Anton-Augustsson/power-tool-workbench/cad/sorting-boxes/stl/2x4.stl

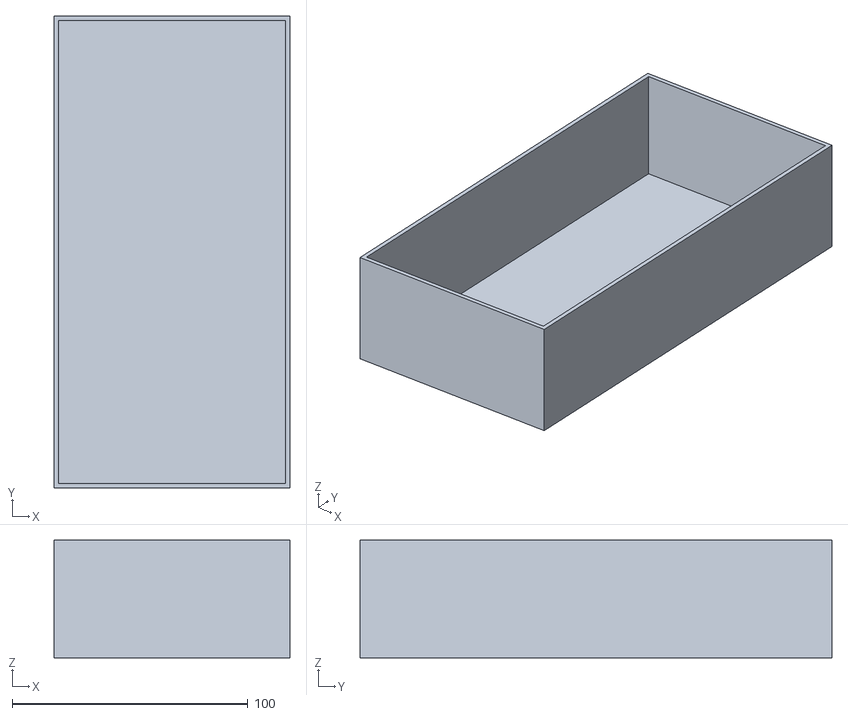
[picture p17: CAD file, 2020-06-16]
cad/sorting-boxes/stl/2x4.stl
100.0 x 200.0 x 50.0
