Anton-Augustsson/power-tool-workbench/cad/sorting-boxes/stl/4x4.stl

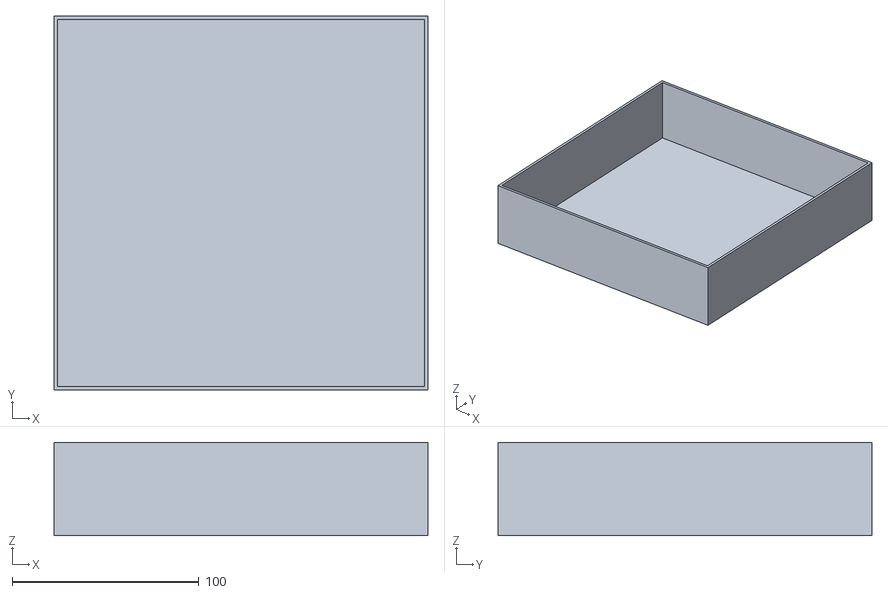
[picture p19: CAD file, 2020-06-16]
cad/sorting-boxes/stl/4x4.stl
200.0 x 200.0 x 50.0
