Anton-Augustsson/power-tool-workbench/cad/sorting-boxes/stl/3x3.stl

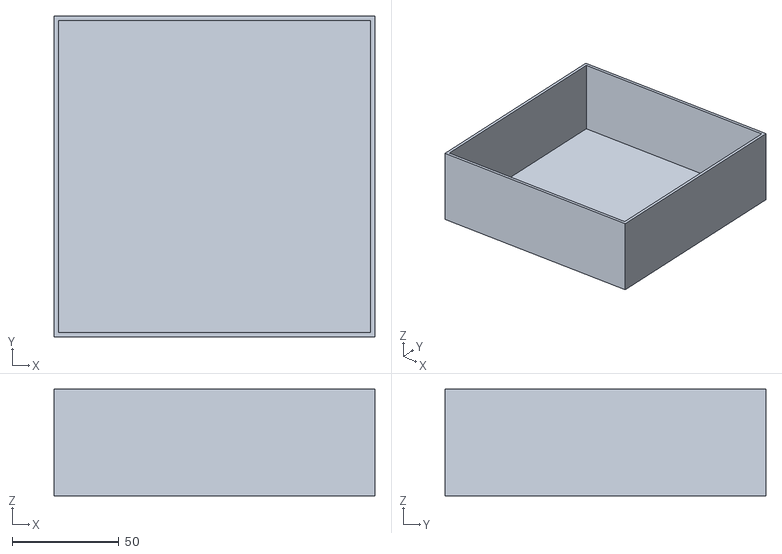
[picture p20: CAD file, 2020-06-16]
cad/sorting-boxes/stl/3x3.stl
150.0 x 150.0 x 50.0
