Anton-Augustsson/power-tool-workbench/cad/sorting-boxes/stl/1x4.stl

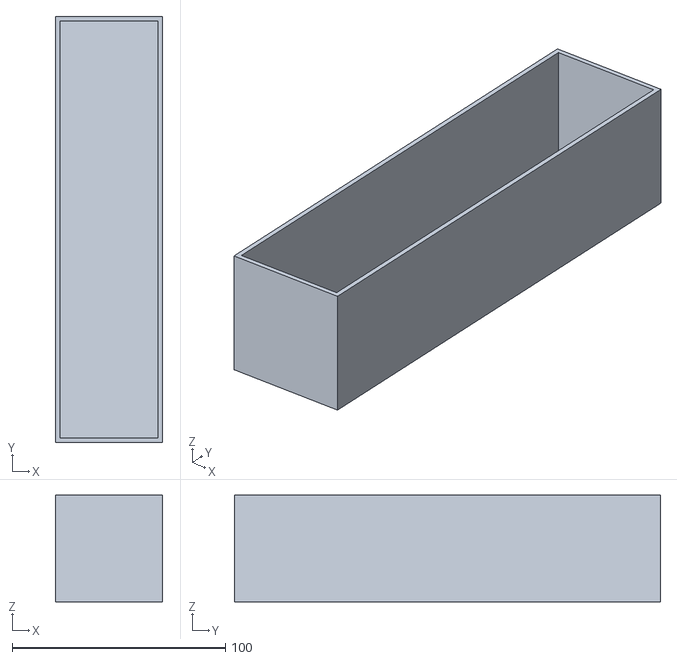
[picture p21: CAD file, 2020-06-16]
cad/sorting-boxes/stl/1x4.stl
50.0 x 200.0 x 50.0
