Anton-Augustsson/power-tool-workbench/cad/module/drawer-storage.scad

/*

    Drawer Storage
    
    By Anton Augustsson


*/

use <simple-drawer.scad>;
use <sliding-shelf.scad>;
use <storage-unit.scad>;

module drawerStorage (
    thickness,
    length,
    width,
    height,
    x,y,z,
    zRotate
    ){
/*
    ---------- Local varibles ---------- 
*/


storageUnitThickness = thickness;
storageUnitWidth     = width;
storageUnitLength    = length;
storageUnitHeight    = height;

thicknessBottom = thickness;
thicknessSide   = thickness;
thicknessFront  = 15;
        
slidingShelfWidth  = (length
        -thickness*2)/2-
        thickness/2;
slidingShelfLength = width
        -thickness*2;
slidingShelfHeight = height/3*2
        +9;

drawerWidth  = slidingShelfWidth;
drawerLength = slidingShelfLength;
drawerHeight = (height-2*thickness)/6;

/*
    ---------- Code ---------- 
*/

translate([
    x,
    y,
    z]) 
rotate([0,0,zRotate])
union () {

storageUnit (
    storageUnitThickness,
    storageUnitWidth,
    storageUnitLength,
    storageUnitHeight,
    0,0,0
    );

// Starting from lower corner    
// 1 Large    
simpleDrawer  (
    thicknessBottom,
    thicknessSide,
    thicknessFront,
    drawerLength,
    drawerWidth,
    drawerHeight*2,
    thickness,
    0,
    thickness
    );

// 2     
simpleDrawer  (
    thicknessBottom,
    thicknessSide,
    thicknessFront,
    drawerLength,
    drawerWidth,
    drawerHeight,
    thickness,
    0,
    thickness+drawerHeight*2
    );

// 3
simpleDrawer  (
    thicknessBottom,
    thicknessSide,
    thicknessFront,
    drawerLength,
    drawerWidth,
    drawerHeight,
    thickness,
    0,
    thickness+drawerHeight*3
    );

// 4
simpleDrawer  (
    thicknessBottom,
    thicknessSide,
    thicknessFront,
    drawerLength,
    drawerWidth,
    drawerHeight,
    thickness,
    0,
    thickness+drawerHeight*4
    );

// 5
simpleDrawer  (
    thicknessBottom,
    thicknessSide,
    thicknessFront,
    drawerLength,
    drawerWidth,
    drawerHeight,
    thickness,
    0,
    thickness+drawerHeight*5
    );



// 6 Large    
simpleDrawer  (
    thicknessBottom,
    thicknessSide,
    thicknessFront,
    drawerLength,
    drawerWidth,
    drawerHeight*2,
    thickness*2
    +slidingShelfWidth,
    0,
    thickness
    );

// 7
simpleDrawer  (
    thicknessBottom,
    thicknessSide,
    thicknessFront,
    drawerLength,
    drawerWidth,
    drawerHeight,
    thickness*2
    +slidingShelfWidth,
    0,
    thickness+drawerHeight*2
    );

// 8
simpleDrawer  (
    thicknessBottom,
    thicknessSide,
    thicknessFront,
    drawerLength,
    drawerWidth,
    drawerHeight,
    thickness*2
    +slidingShelfWidth,
    0,
    thickness+drawerHeight*3
    );    

// 9
simpleDrawer  (
    thicknessBottom,
    thicknessSide,
    thicknessFront,
    drawerLength,
    drawerWidth,
    drawerHeight,
    thickness*2
    +slidingShelfWidth,
    0,
    thickness+drawerHeight*4
    );    

// 10
simpleDrawer  (
    thicknessBottom,
    thicknessSide,
    thicknessFront,
    drawerLength,
    drawerWidth,
    drawerHeight,
    thickness*2
    +slidingShelfWidth,
    0,
    thickness+drawerHeight*5
    );    

}}
    
/*
    ---------- Example ---------- 
*/


standardSheathingWidth = 1220; 
standardSheathingLength = 2440;

mdfTopThickness = 19;
plywoodTopThickness = 12;

// Side protection for ply and mdf
edgeTopThickness = 20; 
edgeTopWidth = 167;
edgeTopLengthX = standardSheathingLength
    +2*edgeTopThickness;
edgeTopLengthY = standardSheathingWidth
    +2*edgeTopThickness;

// 4 list betweend mdf and ply (Pine)
listTopThickness = 20; 
listTopWidth = 80;
listTopLengthX = standardSheathingLength/4
    -listTopThickness;
listTopLengthY = standardSheathingWidth;

// 6 legs (Pine)
legLength = 900
    -plywoodTopThickness
    -mdfTopThickness
    -listTopWidth;
legWidth = 69;
legThickness = 42;

// 3 bottom list (Pine)
listBottomThickness = 20; 
listBottomWidth1 = 60;
listBottomWidth2 = listBottomWidth1
    -plywoodTopThickness;
listBottomLengthX = standardSheathingLength;
listBottomLengthY = standardSheathingWidth;
listBottomLengthY2 = standardSheathingWidth
    +listBottomThickness*2;
bottomHeight = 100;

storageUnitLength=standardSheathingLength/2
    -legThickness*3/2;
storageUnitWidth=400;  
storageUnitHeight=(900-edgeTopWidth)
    -(bottomHeight+listBottomWidth2);
storageUnitThickness=12;


thickness = storageUnitThickness;

length = storageUnitLength;
width  = storageUnitWidth;
height = storageUnitHeight;


x=0;
y=0;
z=0;
zRotate=180;

drawerStorage (
    thickness,
    length,
    width,
    height,
    x,y,z,
    zRotate
    );
