Anton-Augustsson/power-tool-workbench/cad/sorting-boxes/stl.scad

/*

    Storage box
    
    By Anton Augustsson
    
    
*/


// import module
use <SortBox.scad>;

SortBox (4,4);
